tejgrewal/SmartDial/include/driver.h

// ...existing code...
#ifndef DRIVER_H
#define DRIVER_H

// Seeed XIAO round display (GC9A01)
#define BOARD_SCREEN_COMBO 501

// Ensure TFT_eSPI gets all TFT_* macros (TFT_DRIVER, TFT_WIDTH, TFT_HEIGHT, pin defs).
// If your Seeed_GFX copy uses a different Setup file name, change the include below.
#include <User_Setups/Setup501_Seeed_XIAO_Round_Display.h>

#endif // DRIVER_H
